BortSerg/ESP8266-Meteo-Station/Weather_Station_NoRTC_14_07_2022/OTA_Update.ino

 void OTA_Update()
 {
  //===============Обновление через ОТА=========================
 
  // строчка для номера порта по умолчанию
  // можно вписать «8266»:
  // ArduinoOTA.setPort(8266);

  // строчка для названия хоста по умолчанию;
  // можно вписать «esp8266-[ID чипа]»:
  // ArduinoOTA.setHostname("myesp8266");

  // строчка для аутентификации
  // (по умолчанию никакой аутентификации не будет):
  // ArduinoOTA.setPassword((const char *)"123");

  ArduinoOTA.onStart([]() {
    Serial.println("Start");  //  "Начало OTA-апдейта"
  });
  ArduinoOTA.onEnd([]() {
    Serial.println("\nEnd");  //  "Завершение OTA-апдейта"
  });
  ArduinoOTA.onProgress([](unsigned int progress, unsigned int total) {
    Serial.printf("Progress: %u%%\r", (progress / (total / 100)));
  });
  ArduinoOTA.onError([](ota_error_t error) {
    Serial.printf("Error[%u]: ", error);
    if (error == OTA_AUTH_ERROR) Serial.println("Auth Failed");
    //  "Ошибка при аутентификации"
    else if (error == OTA_BEGIN_ERROR) Serial.println("Begin Failed");
    //  "Ошибка при начале OTA-апдейта"
    else if (error == OTA_CONNECT_ERROR) Serial.println("Connect Failed");
    //  "Ошибка при подключении"
    else if (error == OTA_RECEIVE_ERROR) Serial.println("Receive Failed");
    //  "Ошибка при получении данных"
    else if (error == OTA_END_ERROR) Serial.println("End Failed");
    //  "Ошибка при завершении OTA-апдейта"
  });
  ArduinoOTA.begin();
  Serial.println("Ready");  //  "Готово"
  //Serial.println(WiFi.localIP());

  //=============================================================================
  }
